AhmadHaniF1145/Projek-Mikrokontroller-Sensor-Gas/Assets/PCB Design/Final/PCB 3D Model/3D Image dengan komponen (tidak lengkap).png

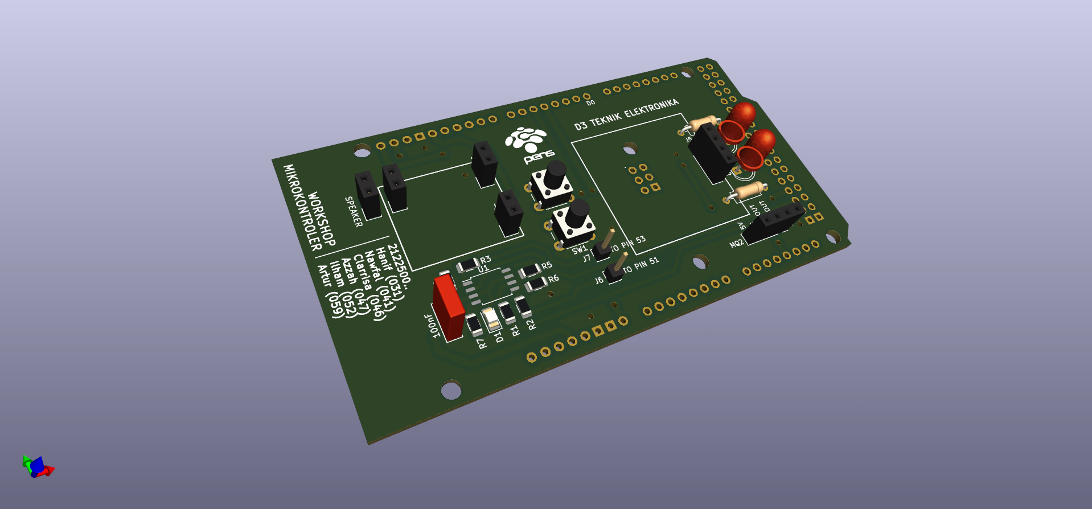
Assets/PCB Design/Final/PCB 3D Model/3D Image dengan komponen (tidak lengkap).png
