AhmadHaniF1145/Projek-Mikrokontroller-Sensor-Gas/Assets/PCB Design/Final/TOP.JPG

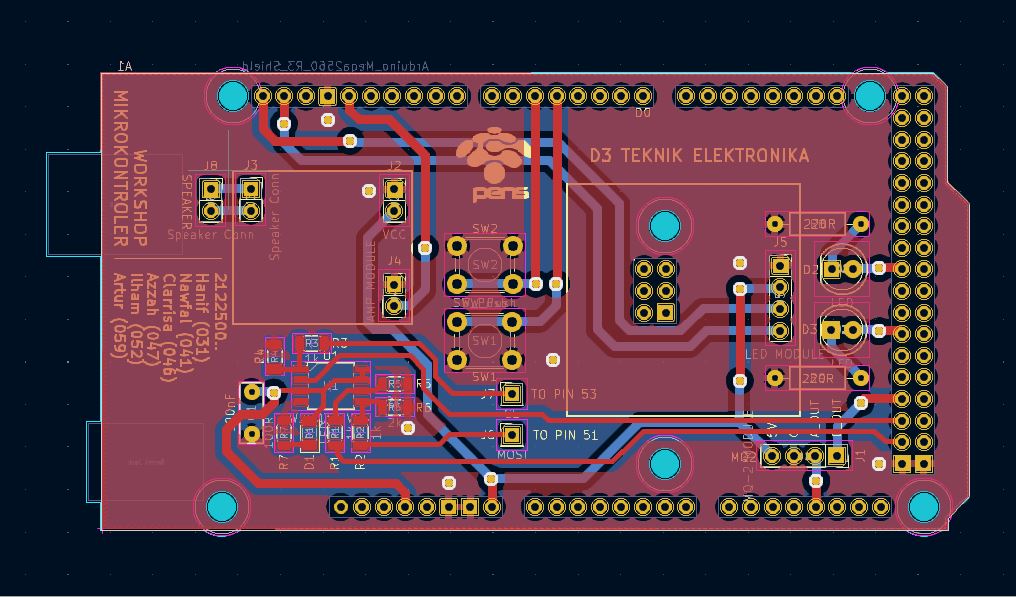
Assets/PCB Design/Final/TOP.JPG
