AhmadHaniF1145/Projek-Mikrokontroller-Sensor-Gas/Assets/PCB Design/Pre/3D PCB Design/1.jpg

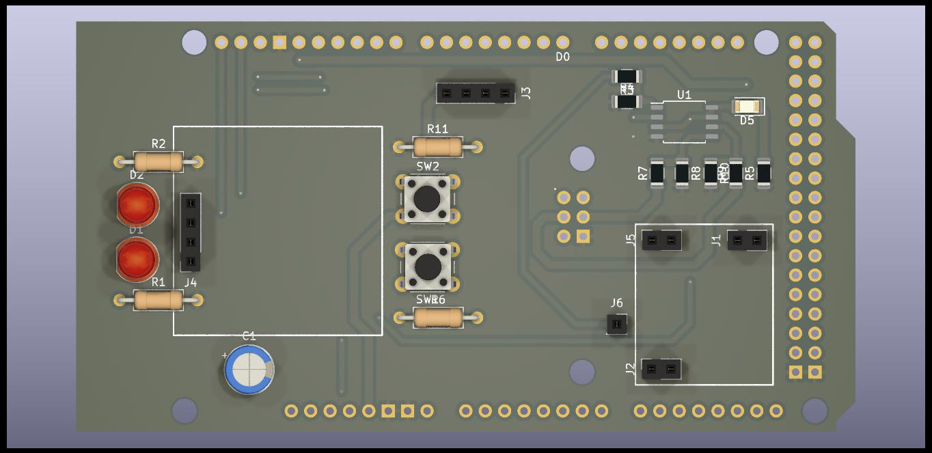
Assets/PCB Design/Pre/3D PCB Design/1.jpg
