AhmadHaniF1145/Projek-Mikrokontroller-Sensor-Gas/Assets/PCB Design/Pre/PCB TOP.JPG

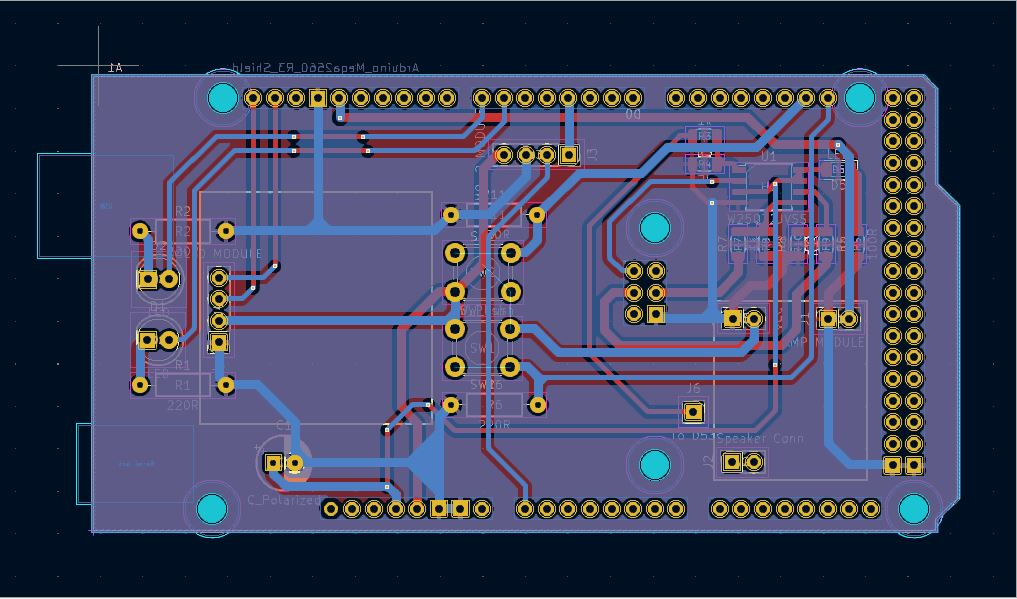
Assets/PCB Design/Pre/PCB TOP.JPG
