AhmadHaniF1145/Projek-Mikrokontroller-Sensor-Gas/Assets/Simulation and Schematic Design/Configuration.jpg

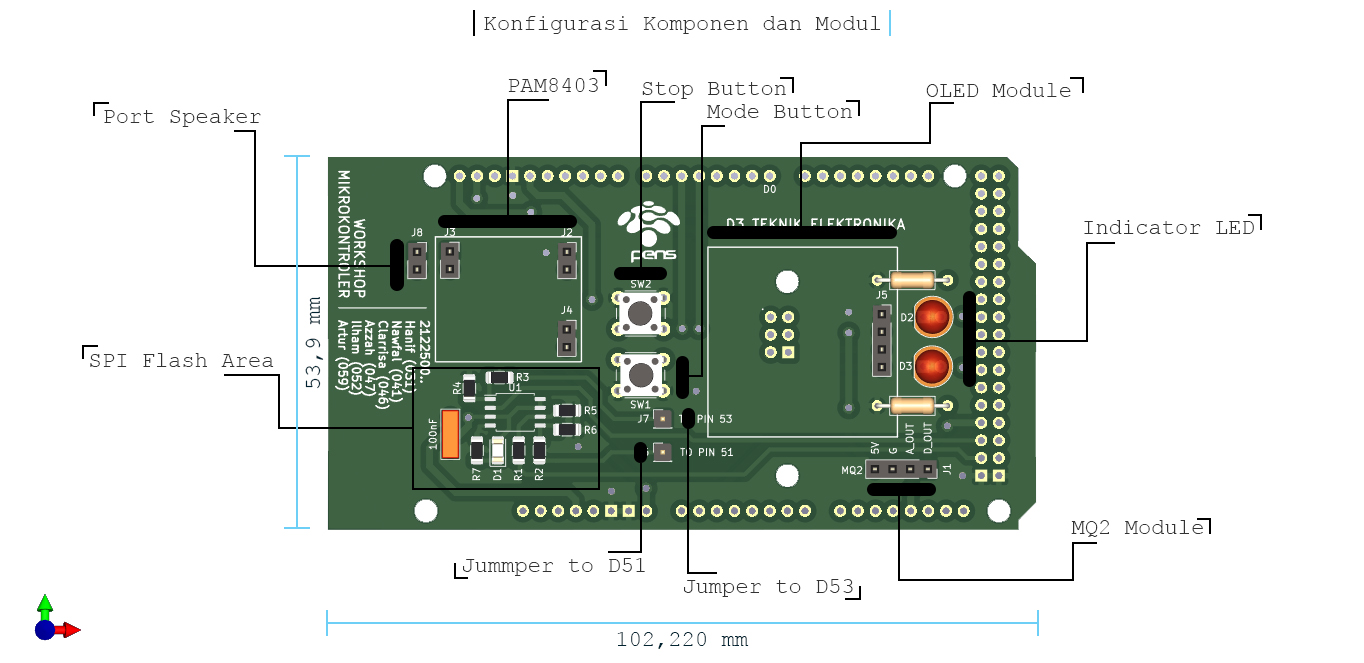
Assets/Simulation and Schematic Design/Configuration.jpg
