AhmadHaniF1145/Projek-Mikrokontroller-Sensor-Gas/Assets/Simulation and Schematic Design/Schematic - Pre.jpg

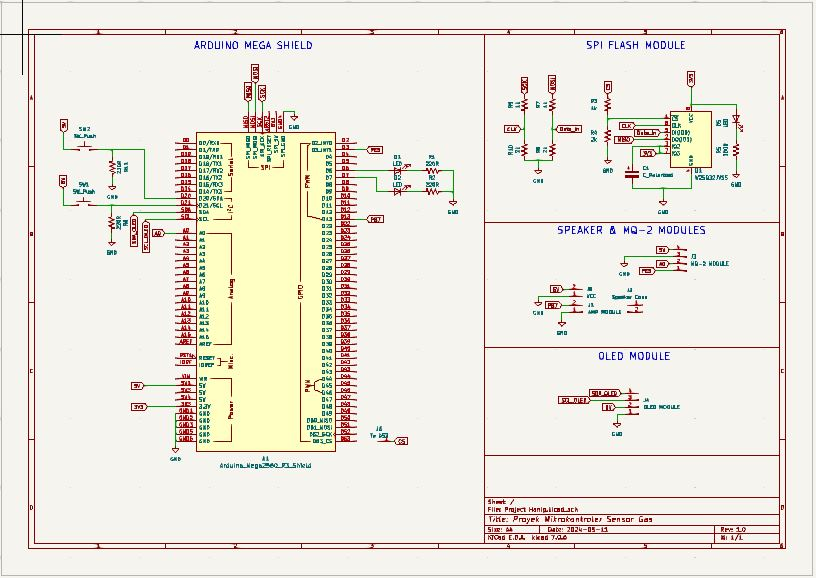
Assets/Simulation and Schematic Design/Schematic - Pre.jpg
