AhmadHaniF1145/Projek-Mikrokontroller-Sensor-Gas/Audio_Project/audio1/audio1 auda.png

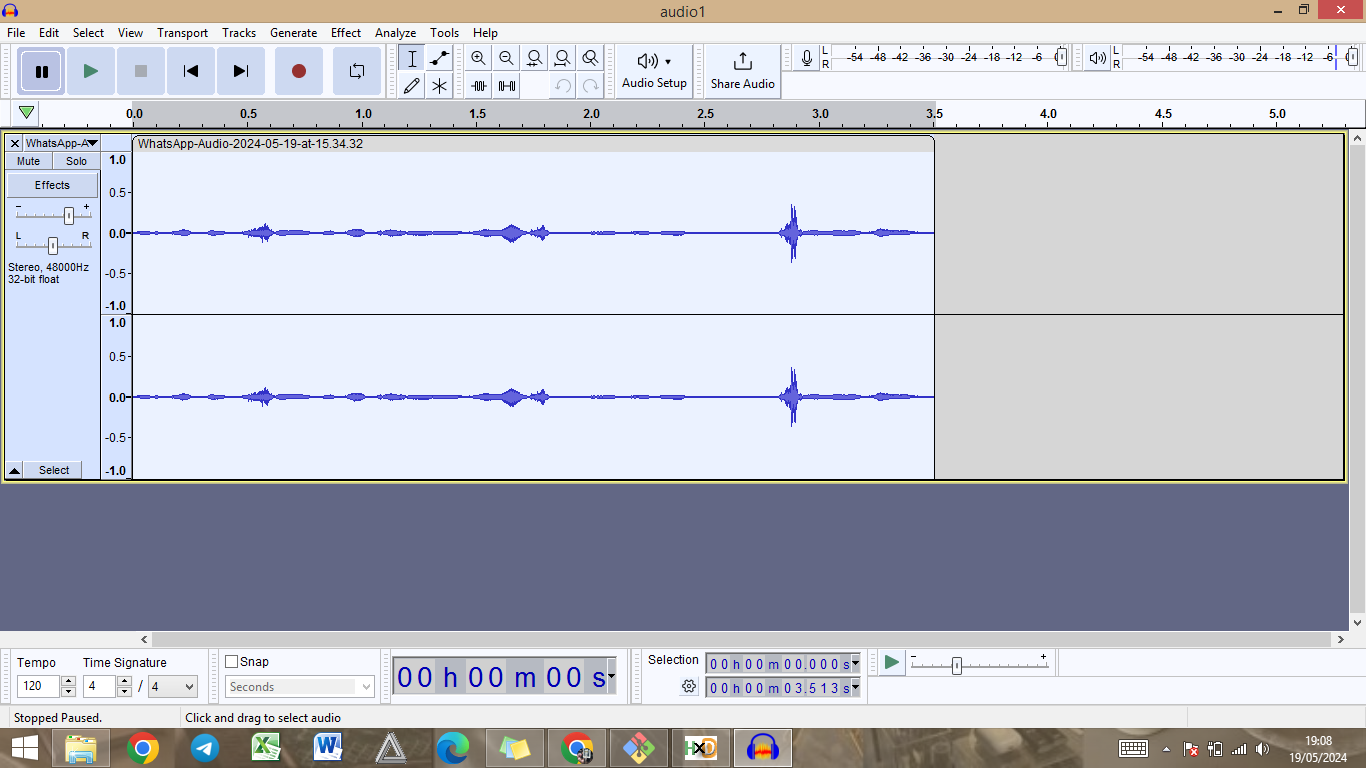
Audio_Project/audio1/audio1 auda.png
