AhmadHaniF1145/Projek-Mikrokontroller-Sensor-Gas/Audio_Project/audio1/audio1 hxd.png

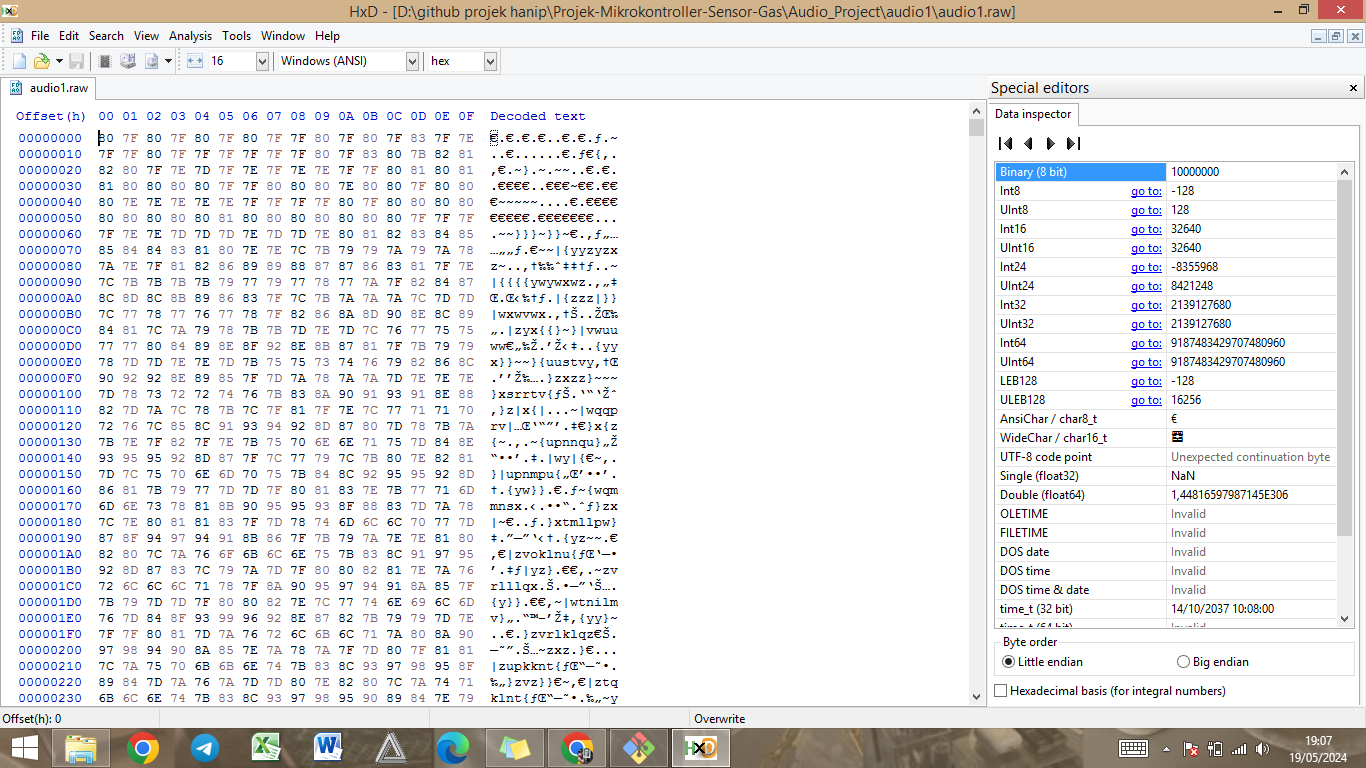
Audio_Project/audio1/audio1 hxd.png
