AhmadHaniF1145/Projek-Mikrokontroller-Sensor-Gas/Audio_Project/audio2/audio2 auda.png

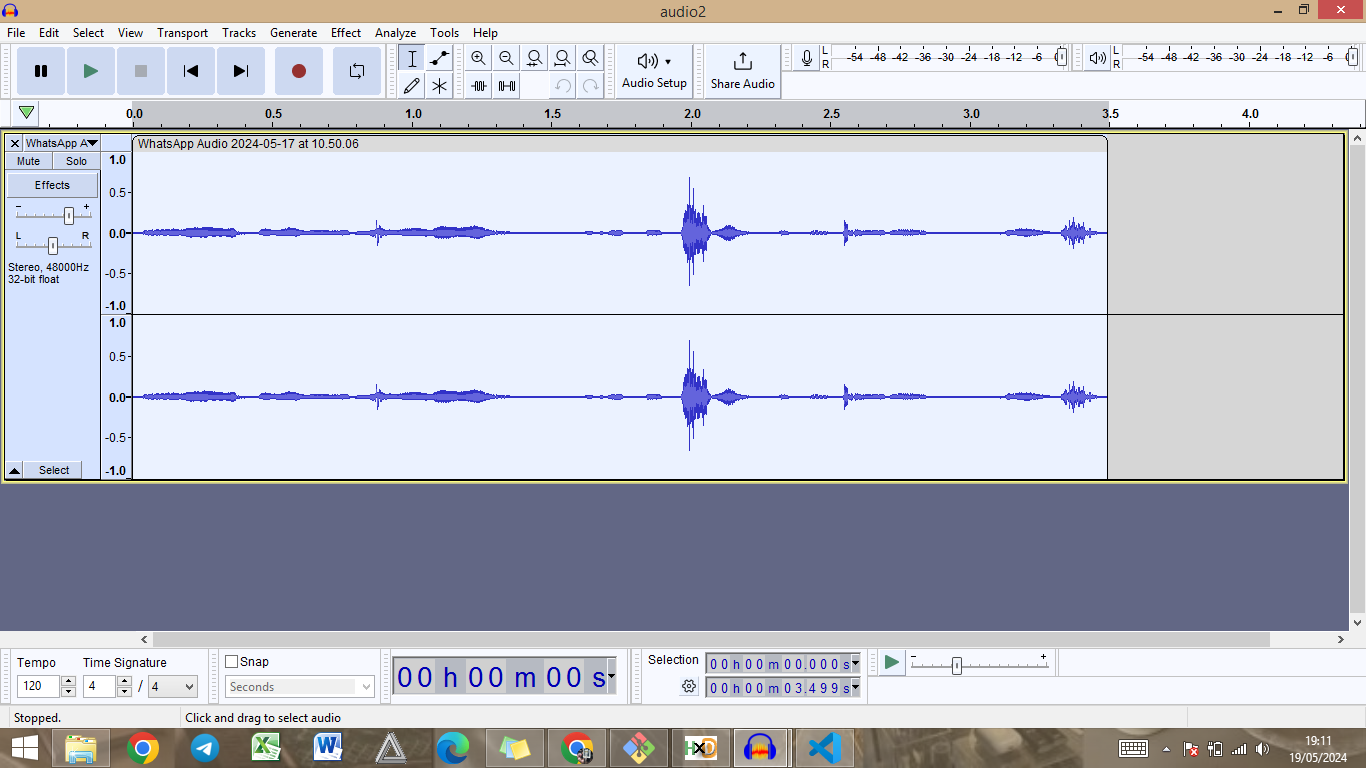
Audio_Project/audio2/audio2 auda.png
