AhmadHaniF1145/Projek-Mikrokontroller-Sensor-Gas/Audio_Project/audio2/audio2 hxd.png

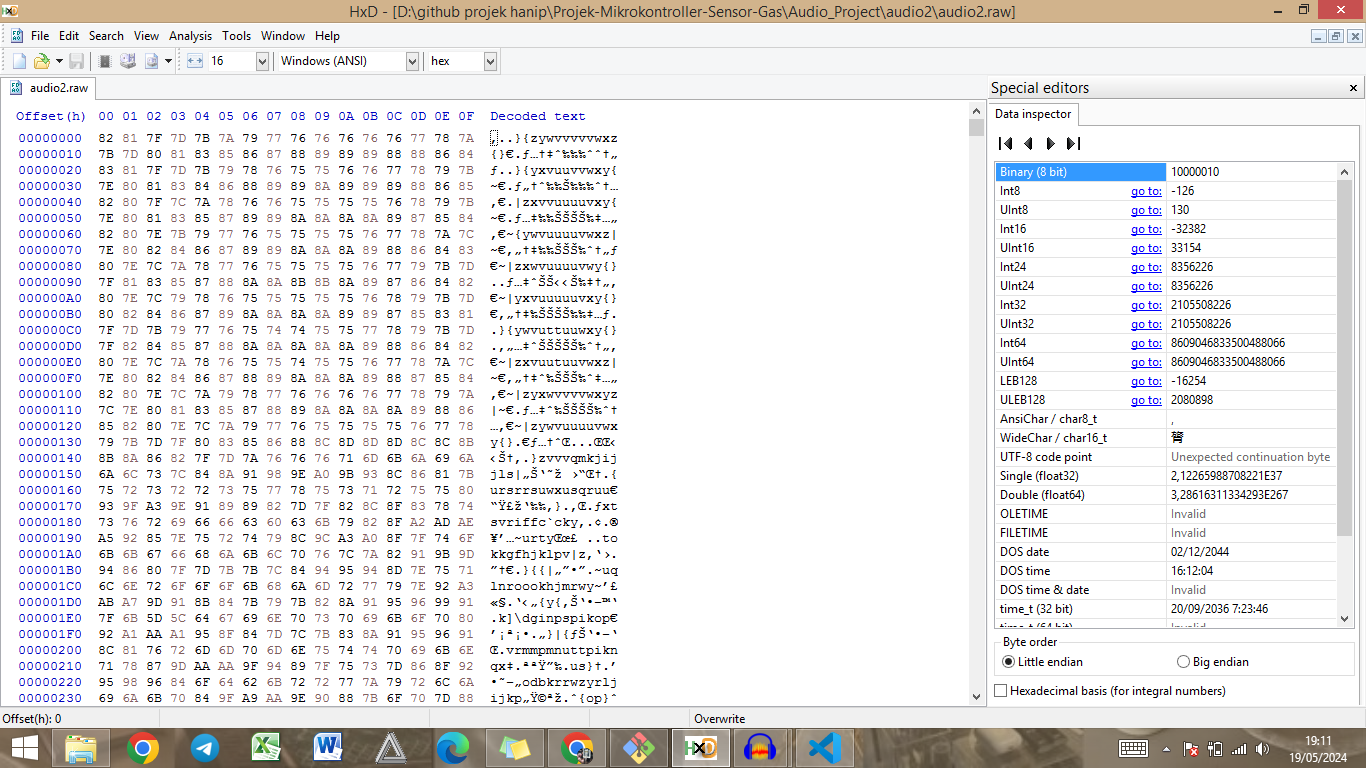
Audio_Project/audio2/audio2 hxd.png
