AhmadHaniF1145/Projek-Mikrokontroller-Sensor-Gas/Desain 3D/Casing 3D Drawing v3.jpg

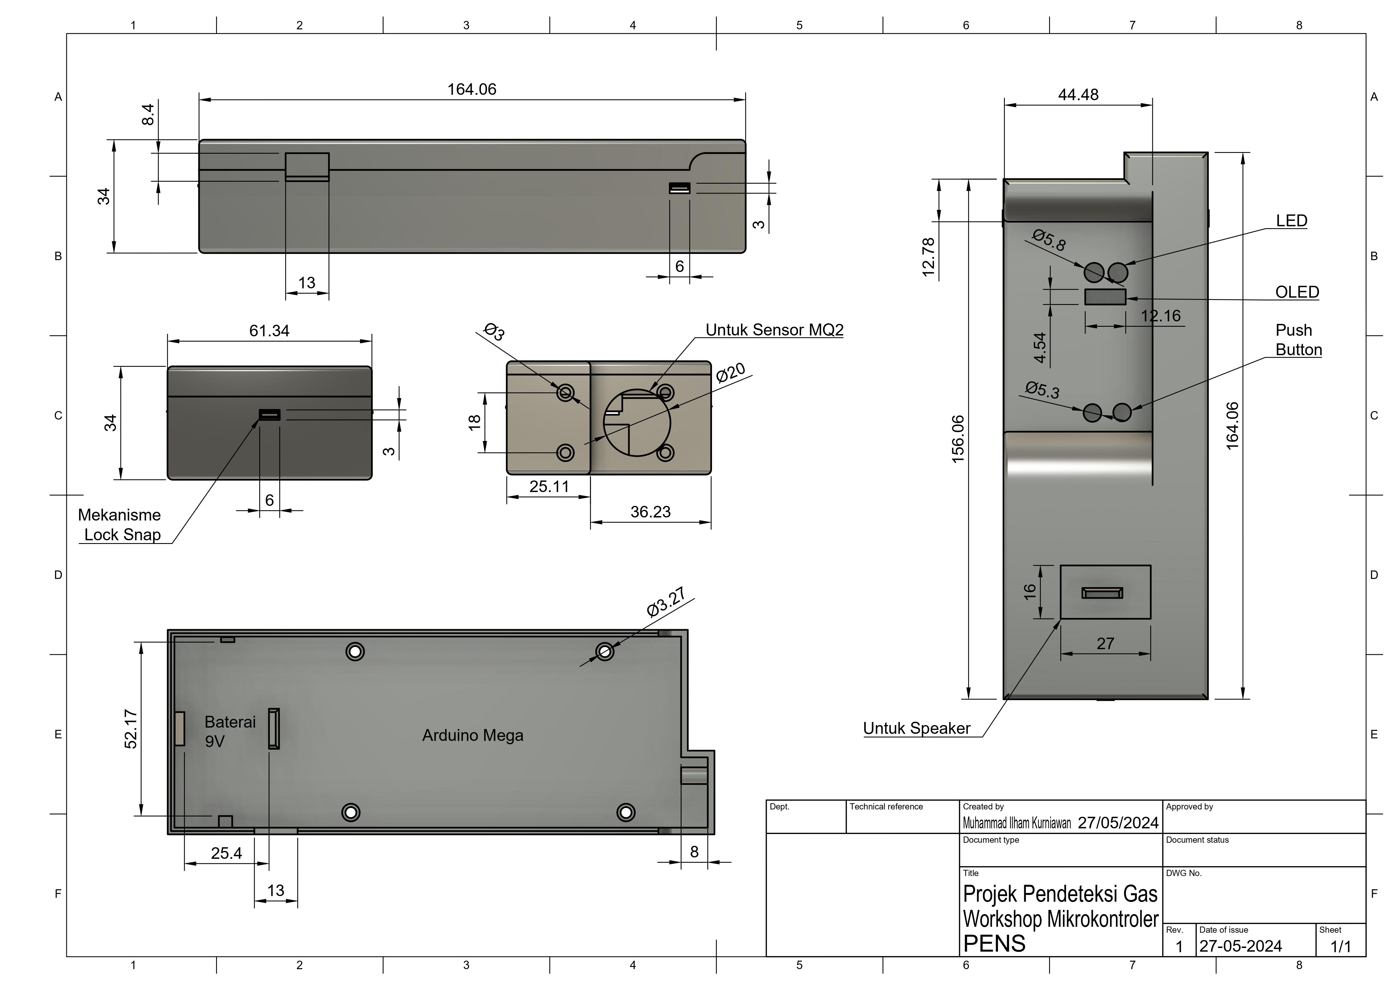
Desain 3D/Casing 3D Drawing v3.jpg
