AhmadHaniF1145/Projek-Mikrokontroller-Sensor-Gas/Desain 3D/Hasil Desain 3D.jpeg

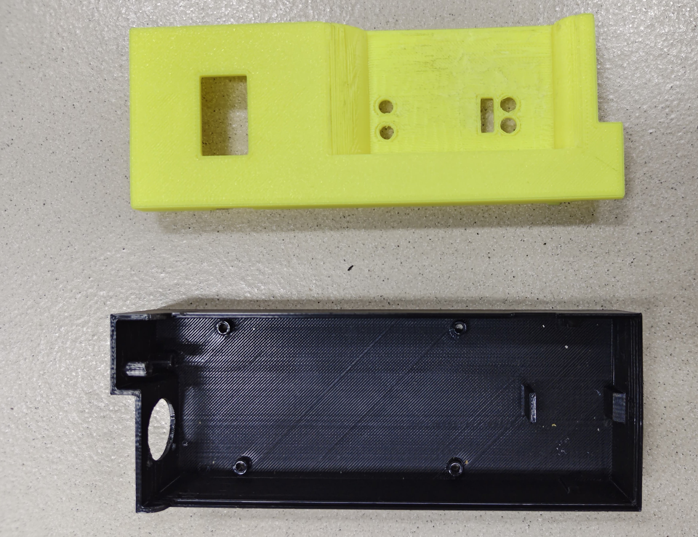
Desain 3D/Hasil Desain 3D.jpeg
