AhmadHaniF1145/Projek-Mikrokontroller-Sensor-Gas/Desain 3D/Prototype 1.png

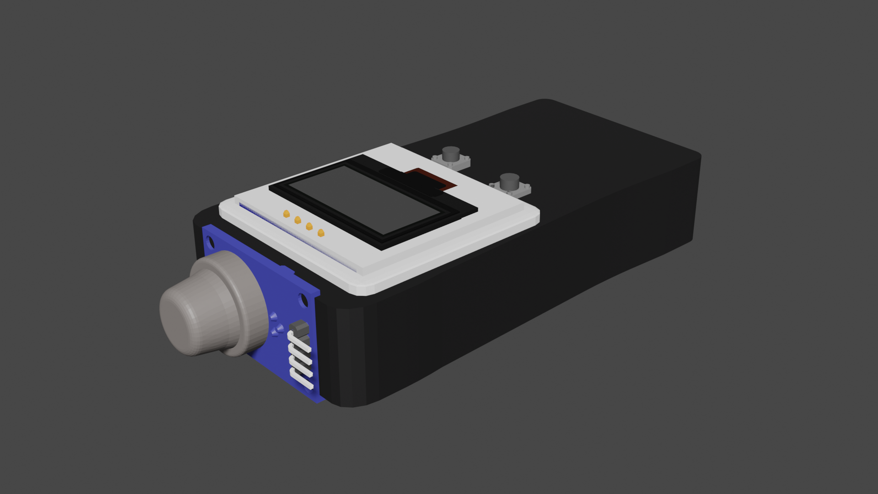
Desain 3D/Prototype 1.png
