AhmadHaniF1145/Projek-Mikrokontroller-Sensor-Gas/Desain 3D/WhatsApp Image 2024-05-21 at 08.23.38.jpeg

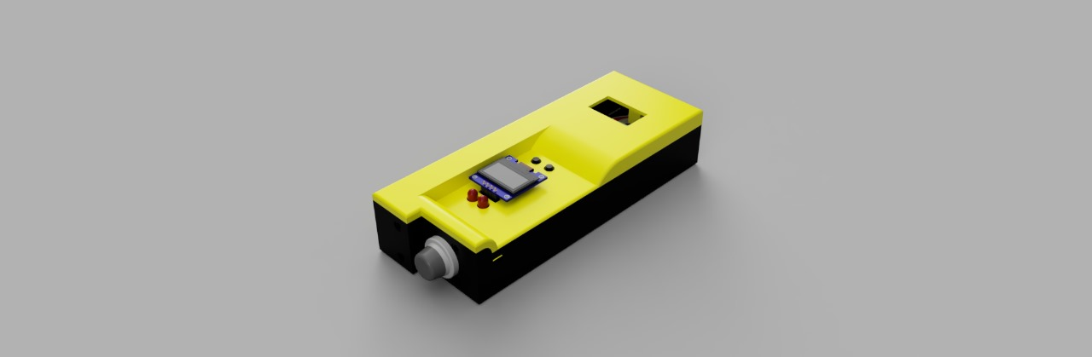
Desain 3D/WhatsApp Image 2024-05-21 at 08.23.38.jpeg
