AhmadHaniF1145/Projek-Mikrokontroller-Sensor-Gas/Dokumentasi/Desain PCB.jpeg

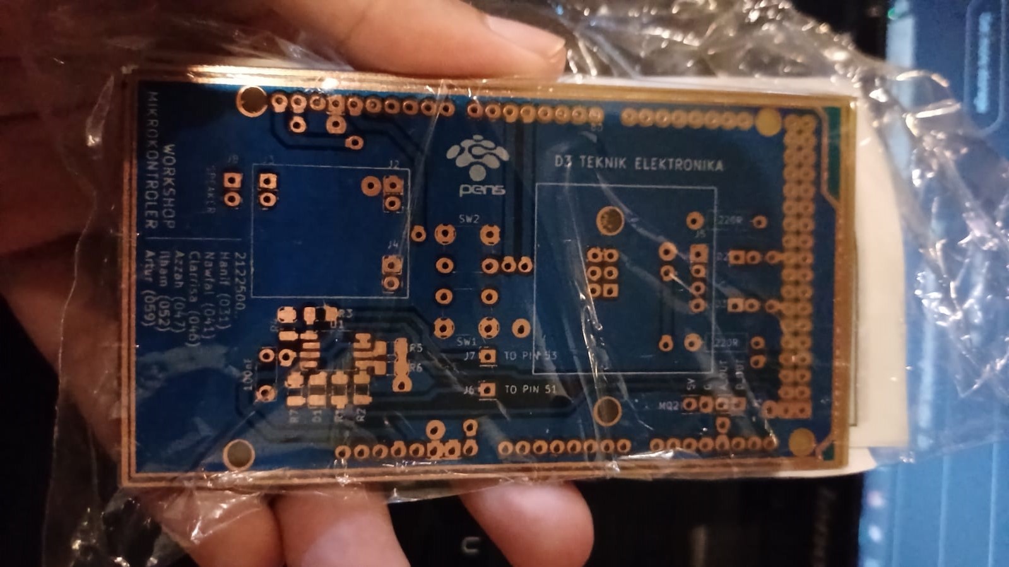
Dokumentasi/Desain PCB.jpeg
