AhmadHaniF1145/Projek-Mikrokontroller-Sensor-Gas/Dokumentasi/Komponen yang Sudah Dibeli.jpeg

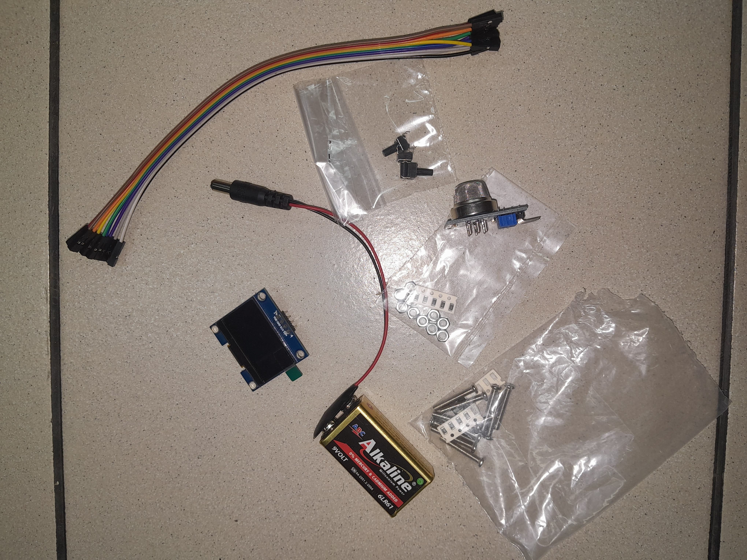
Dokumentasi/Komponen yang Sudah Dibeli.jpeg
