AhmadHaniF1145/Projek-Mikrokontroller-Sensor-Gas/Dokumentasi/Pembuataan Program.jpg

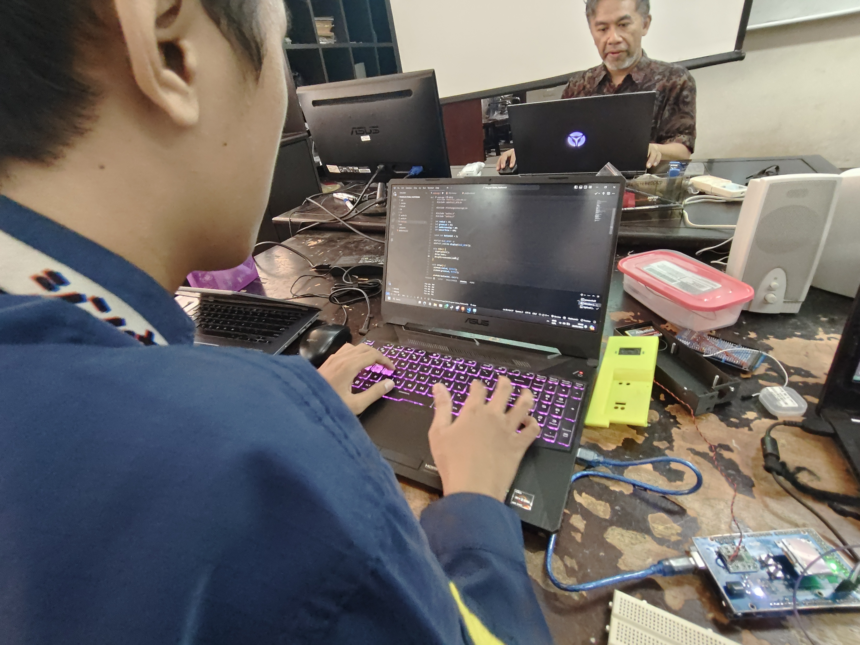
Dokumentasi/Pembuataan Program.jpg
