AhmadHaniF1145/Projek-Mikrokontroller-Sensor-Gas/Dokumentasi/Pembuatan Audio Project.jpeg

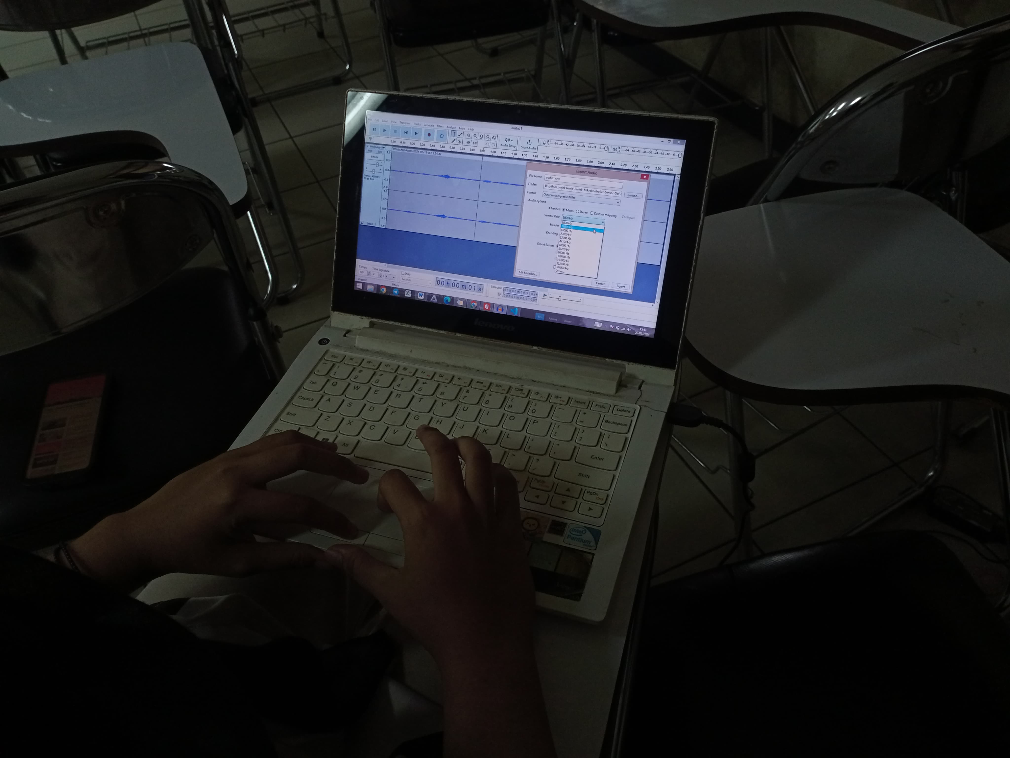
Dokumentasi/Pembuatan Audio Project.jpeg
