AhmadHaniF1145/Projek-Mikrokontroller-Sensor-Gas/Dokumentasi/Pengemasan Project.jpeg

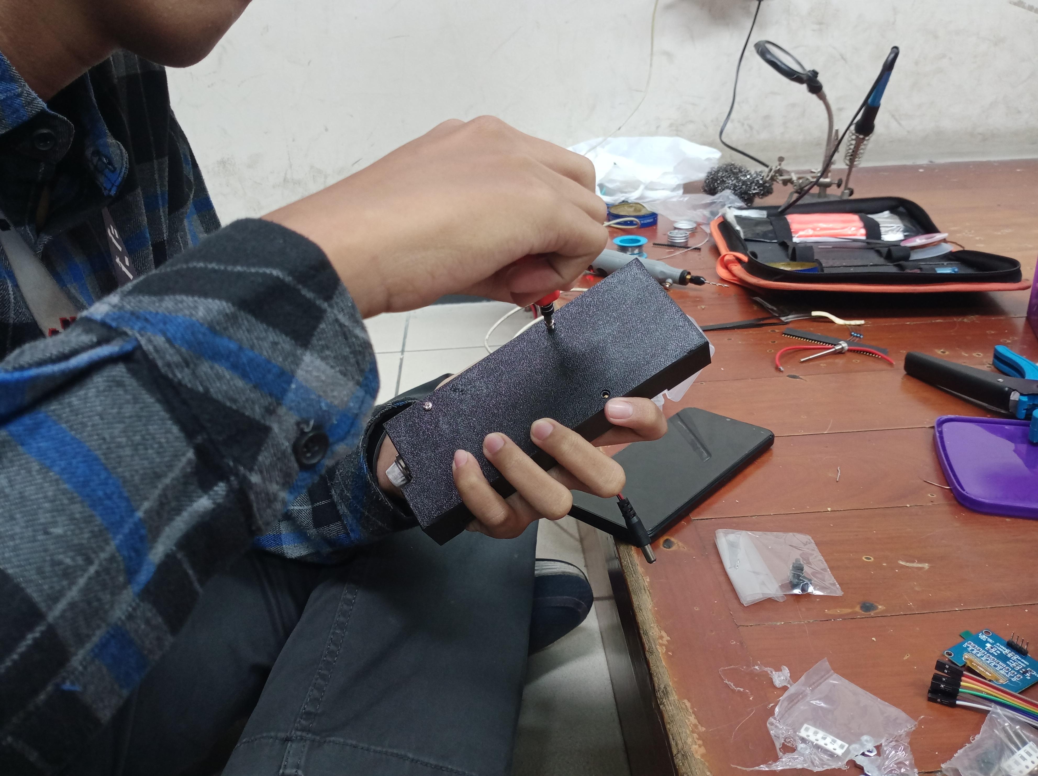
Dokumentasi/Pengemasan Project.jpeg
