AhmadHaniF1145/Projek-Mikrokontroller-Sensor-Gas/Dokumentasi/Pengujian Alat Pada Gas LPG.jpg

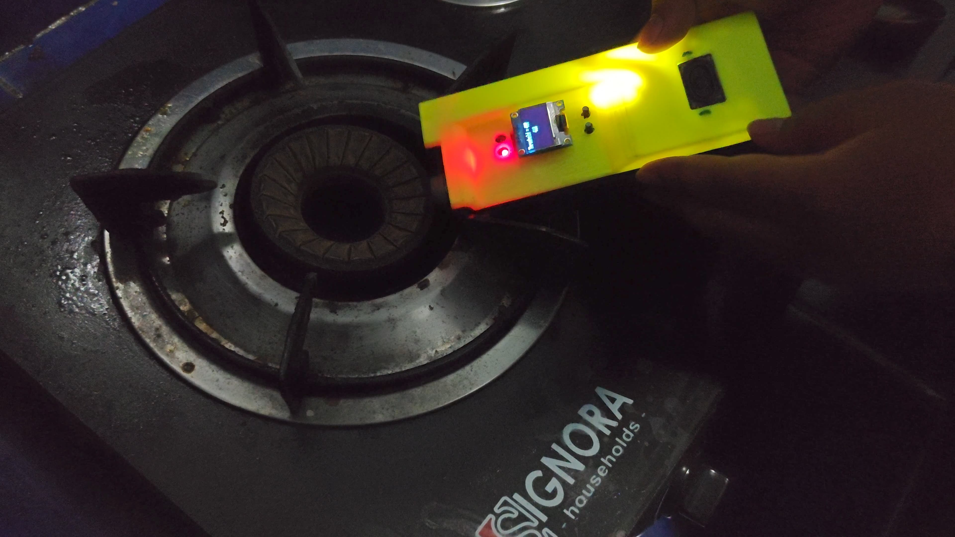
Dokumentasi/Pengujian Alat Pada Gas LPG.jpg
