AhmadHaniF1145/Projek-Mikrokontroller-Sensor-Gas/Dokumentasi/Pengujian Alat.jpg

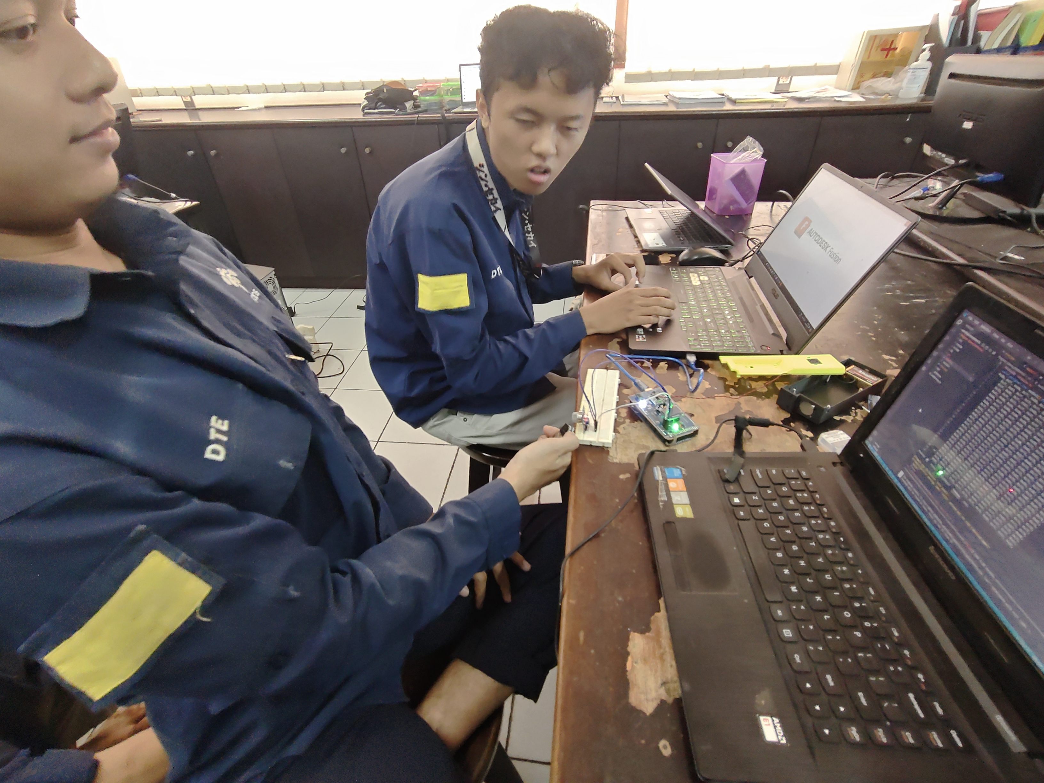
Dokumentasi/Pengujian Alat.jpg
