AhmadHaniF1145/Projek-Mikrokontroller-Sensor-Gas/Dokumentasi/Pengujian Pada Software.jpg

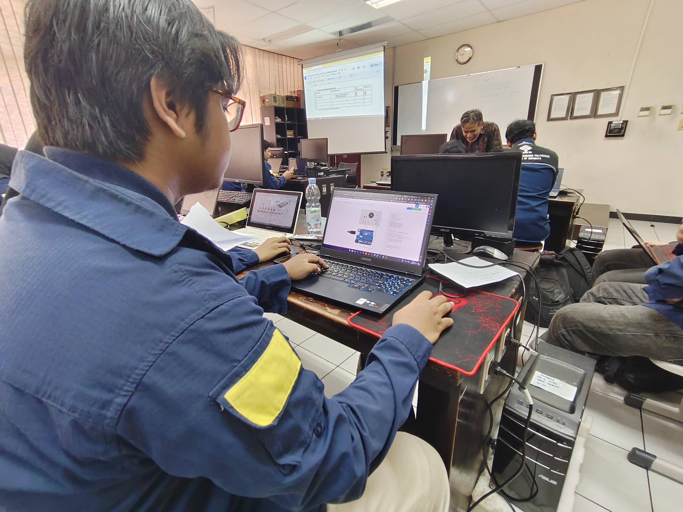
Dokumentasi/Pengujian Pada Software.jpg
