AhmadHaniF1145/Projek-Mikrokontroller-Sensor-Gas/Dokumentasi/Proses Penyolderan.jpeg

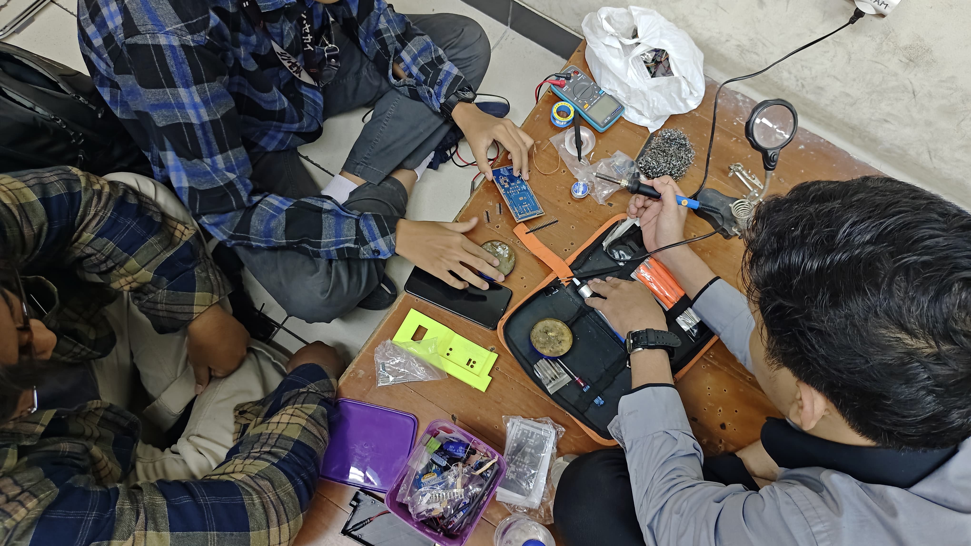
Dokumentasi/Proses Penyolderan.jpeg
