AhmadHaniF1145/Projek-Mikrokontroller-Sensor-Gas/Dokumentasi/Publikasi pada Github.jpeg

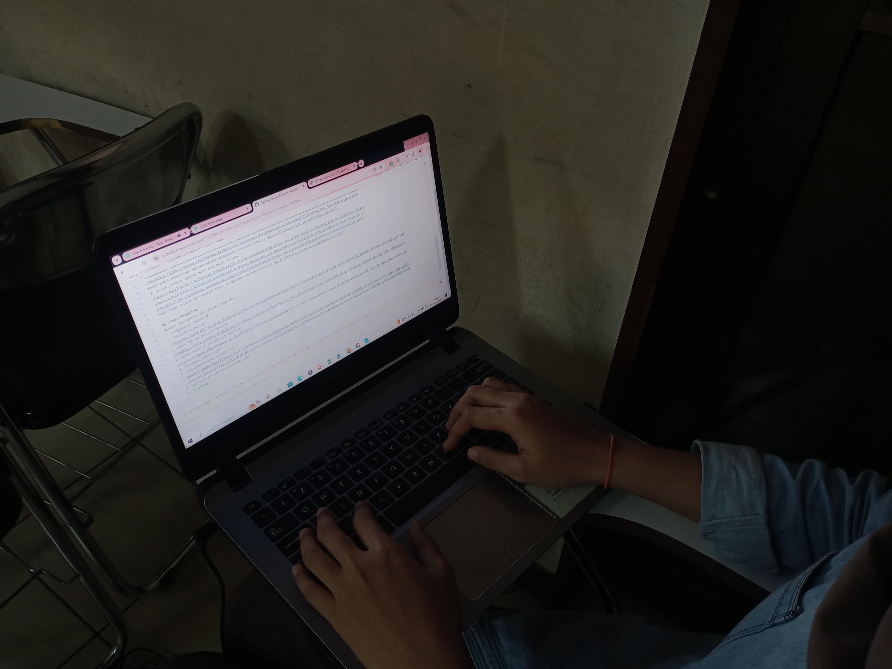
Dokumentasi/Publikasi pada Github.jpeg
