AhmadHaniF1145/Projek-Mikrokontroller-Sensor-Gas/Dokumentasi/Publikasi Thingverse.png

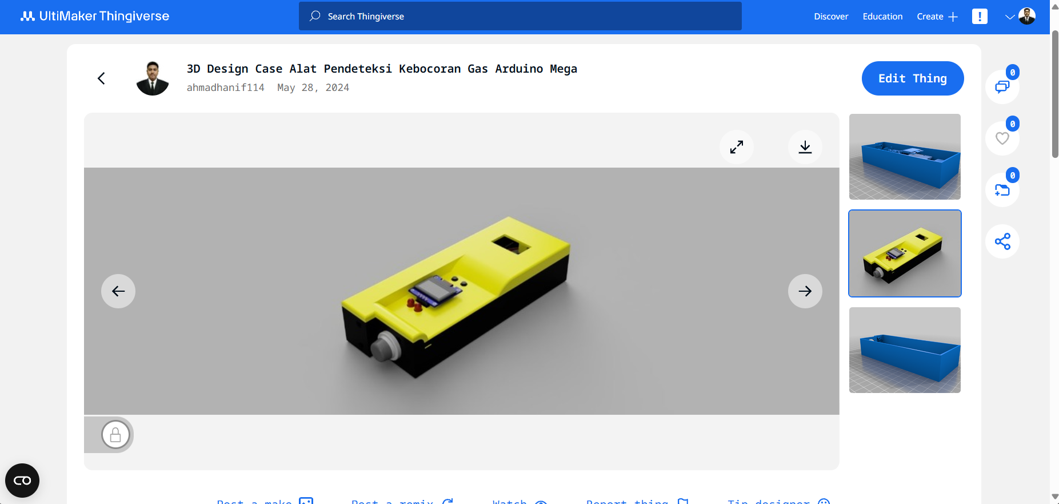
Dokumentasi/Publikasi Thingverse.png
