AhmadHaniF1145/Projek-Mikrokontroller-Sensor-Gas/Dokumentasi/Studi Literatur.jpg

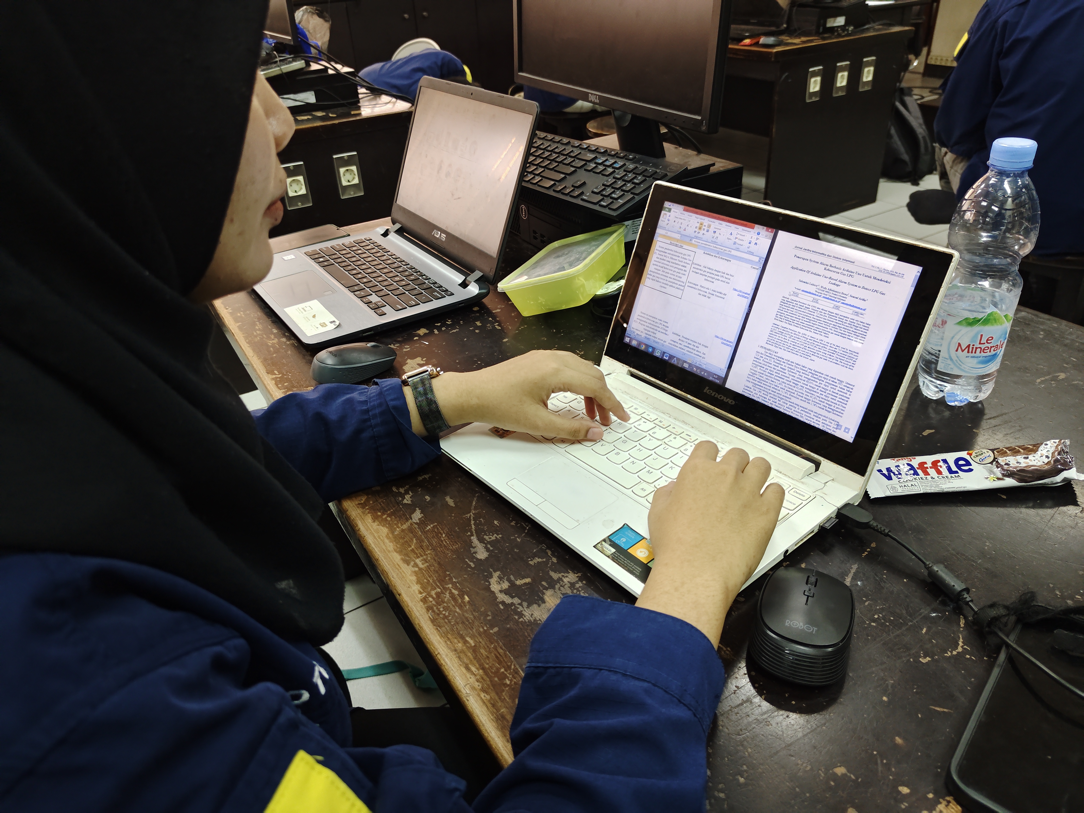
Dokumentasi/Studi Literatur.jpg
