AhmadHaniF1145/Projek-Mikrokontroller-Sensor-Gas/PCB Board/Progress 1/Diagram.JPG

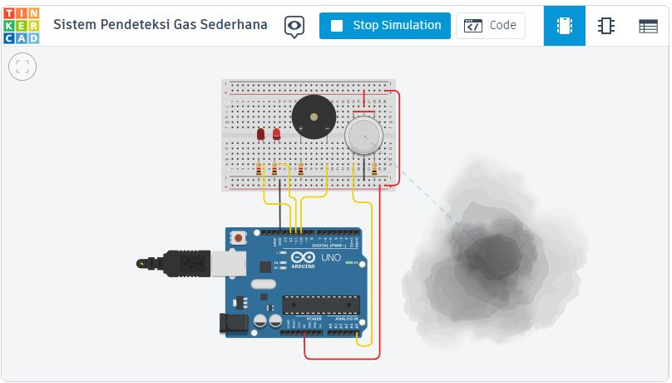
PCB Board/Progress 1/Diagram.JPG
