AhmadHaniF1145/Projek-Mikrokontroller-Sensor-Gas/Desain 3D/Fusion 360 (Manufacture)/Casing_3D_2024-May-12_09-13-18AM-000_CustomizedView19460723771.png

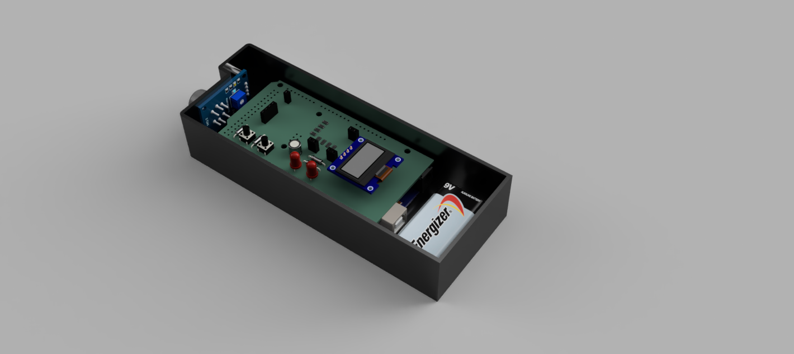
Desain 3D/Fusion 360 (Manufacture)/Casing_3D_2024-May-12_09-13-18AM-000_CustomizedView19460723771.png
