AhmadHaniF1145/Projek-Mikrokontroller-Sensor-Gas/Desain 3D/Fusion 360 (Manufacture)/Casing_3D_2024-May-12_09-14-30AM-000_CustomizedView43419546548.png

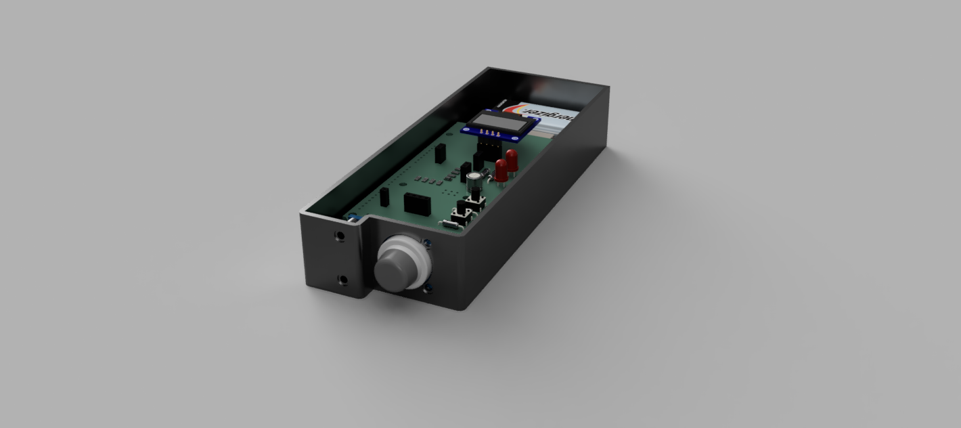
Desain 3D/Fusion 360 (Manufacture)/Casing_3D_2024-May-12_09-14-30AM-000_CustomizedView43419546548.png
