AhmadHaniF1145/Projek-Mikrokontroller-Sensor-Gas/Desain 3D/Fusion 360 (Manufacture)/Casing_3D_2024-May-12_09-15-01AM-000_CustomizedView60361281327.png

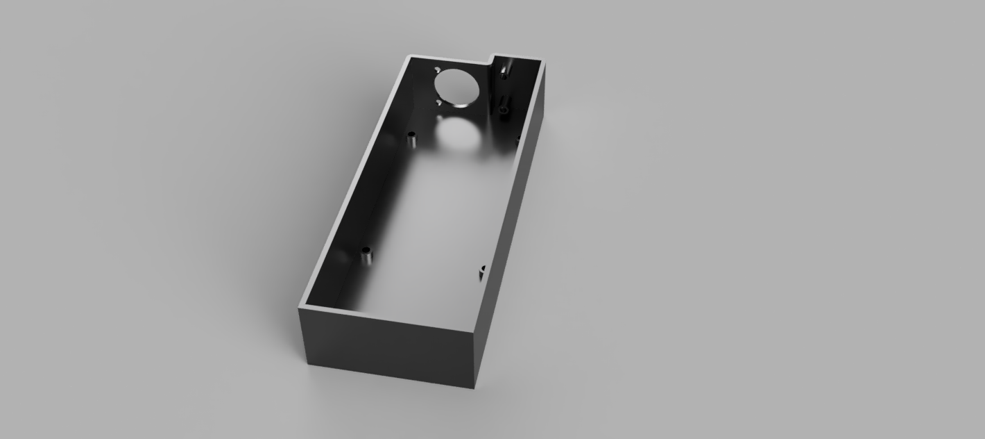
Desain 3D/Fusion 360 (Manufacture)/Casing_3D_2024-May-12_09-15-01AM-000_CustomizedView60361281327.png
