AhmadHaniF1145/Projek-Mikrokontroller-Sensor-Gas/Desain 3D/Fusion 360 (Manufacture)/Screenshot (462).png

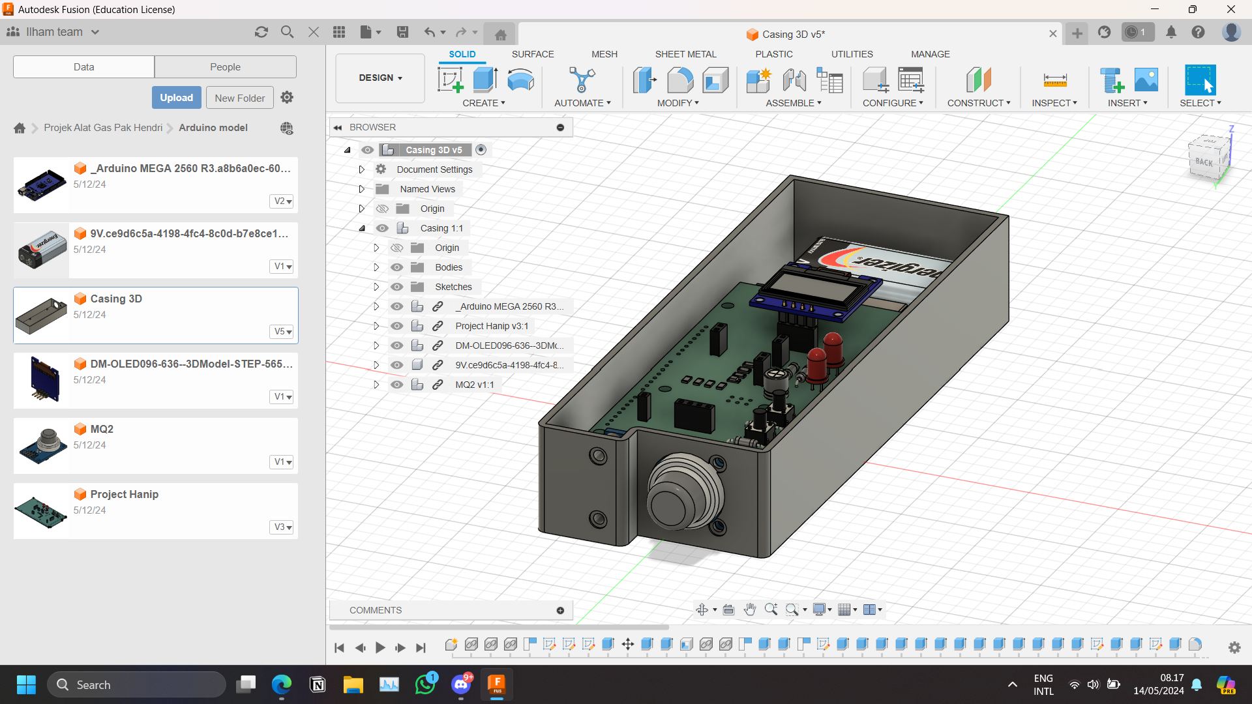
Desain 3D/Fusion 360 (Manufacture)/Screenshot (462).png
