AhmadHaniF1145/Projek-Mikrokontroller-Sensor-Gas/Desain 3D/Fusion 360 (Manufacture)/Screenshot (463).png

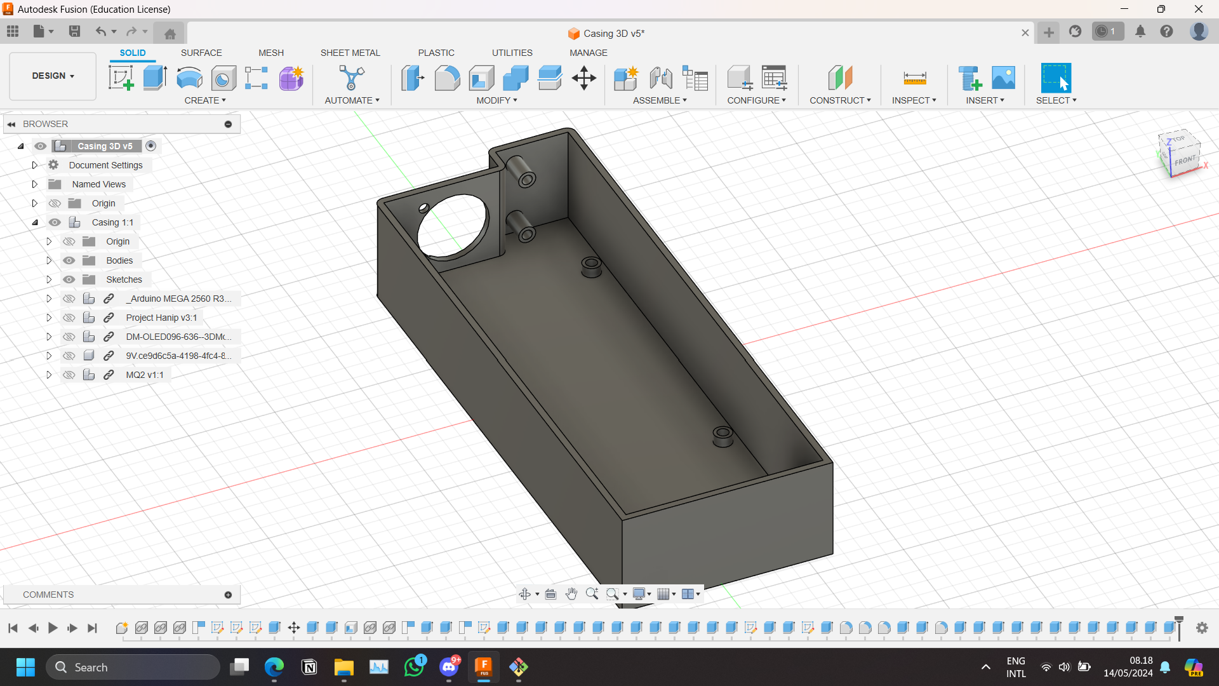
Desain 3D/Fusion 360 (Manufacture)/Screenshot (463).png
