AhmadHaniF1145/Projek-Mikrokontroller-Sensor-Gas/Assets/PCB Print/Rev 0/PCB Top Silk.pdf

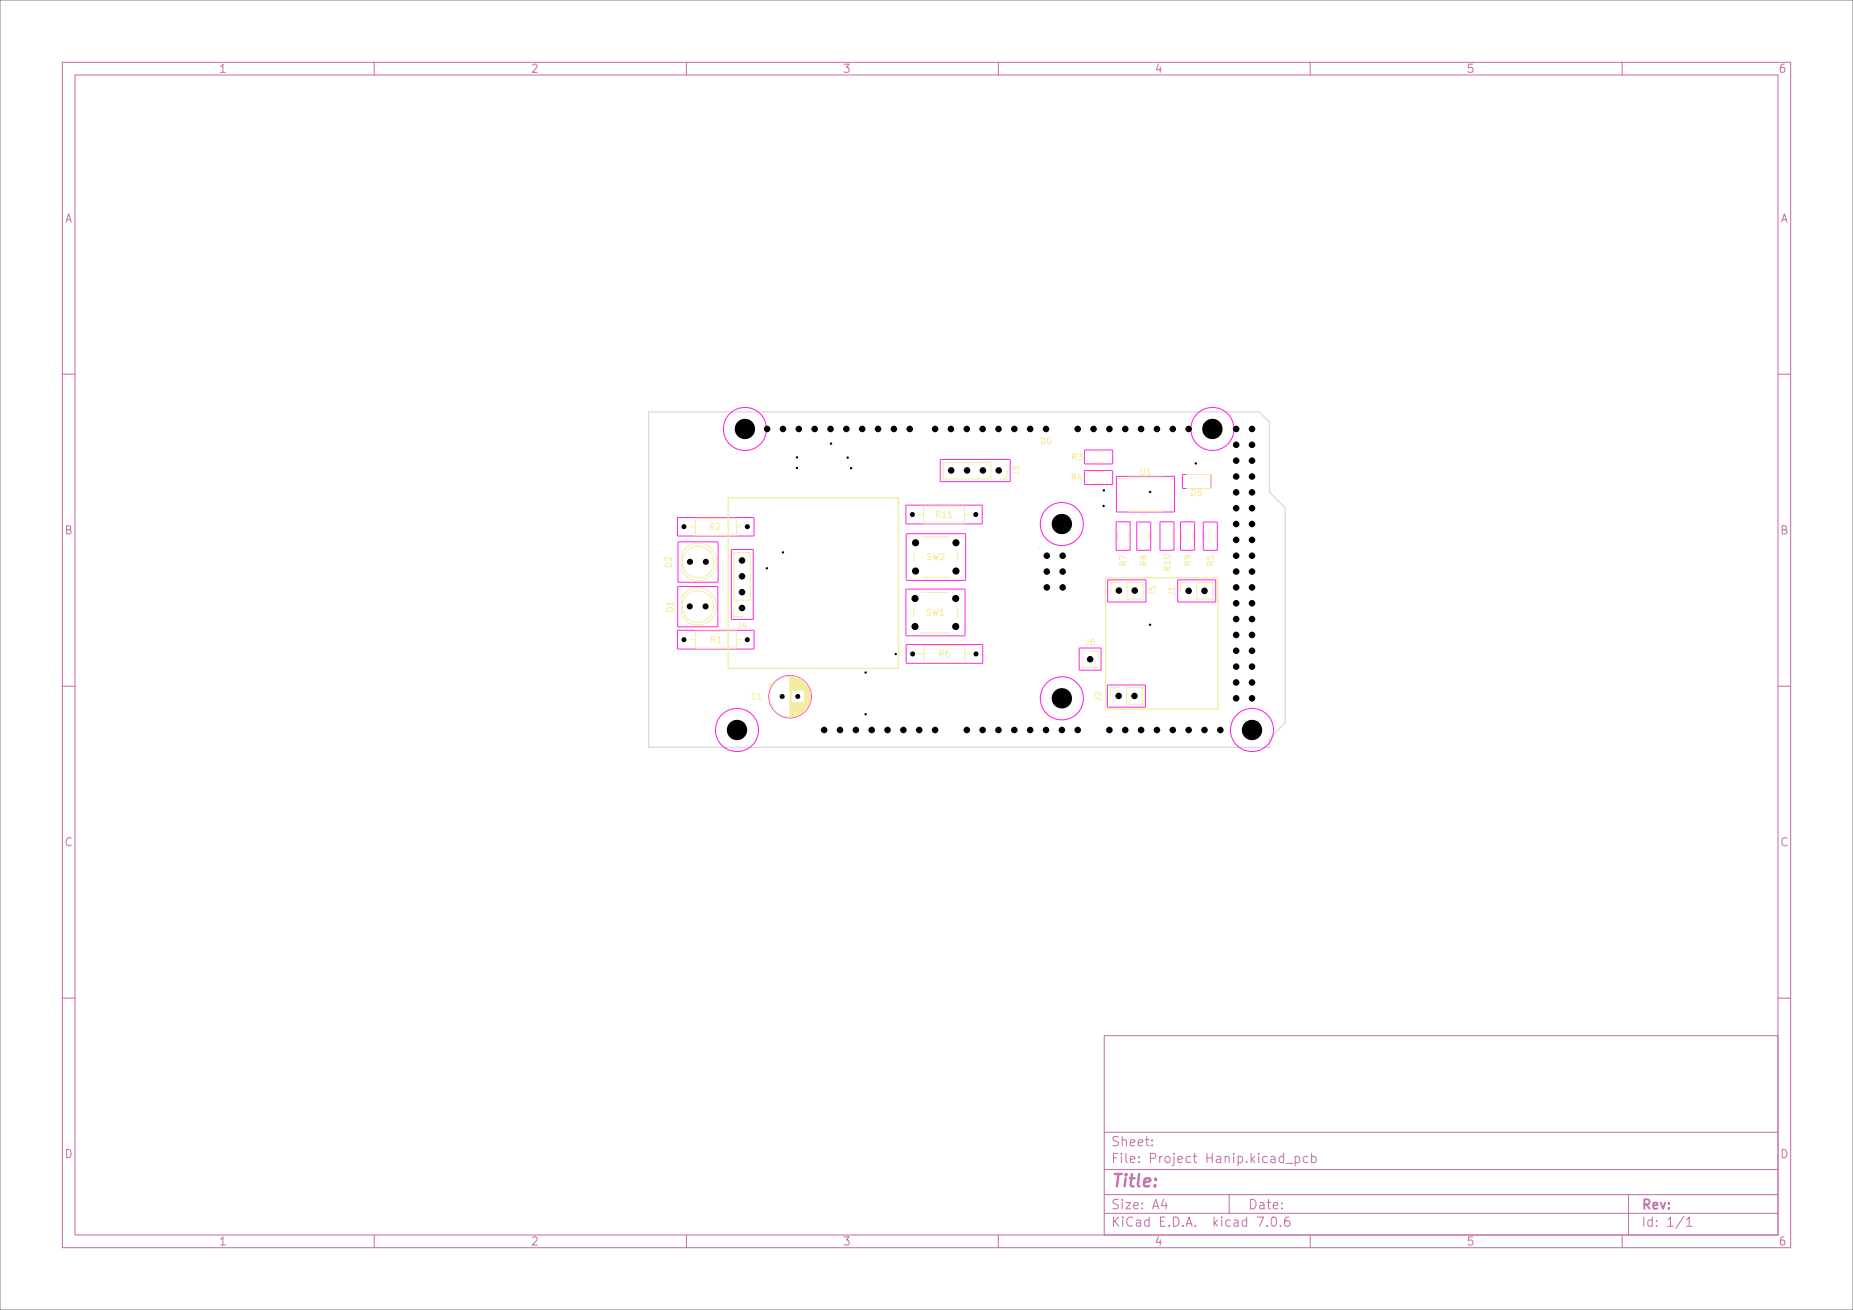
[picture p62: page 1]
