AhmadHaniF1145/Projek-Mikrokontroller-Sensor-Gas/Assets/PCB Print/Rev 0/PCB Top.pdf

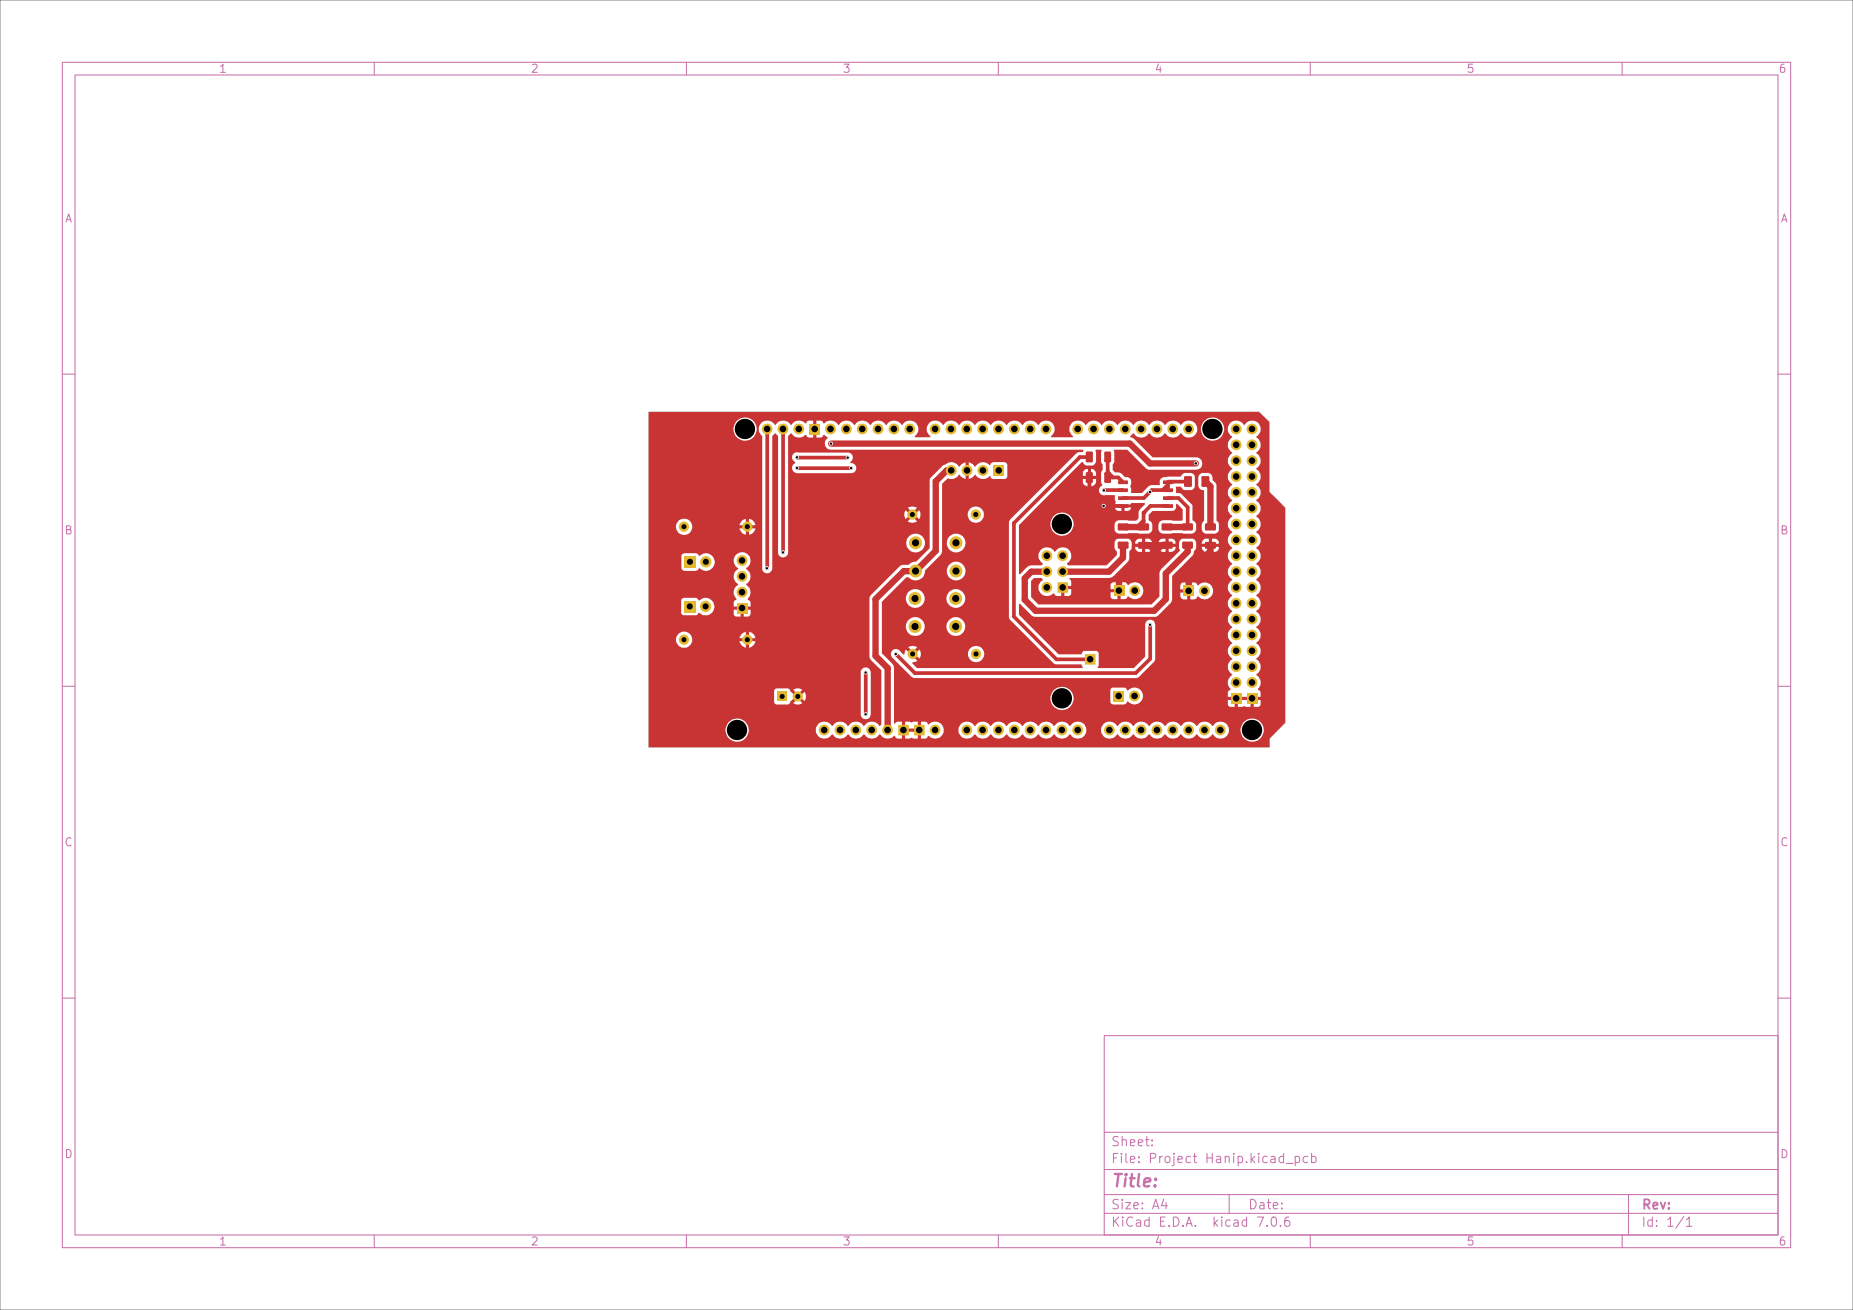
[picture p63: page 1]
