AhmadHaniF1145/Projek-Mikrokontroller-Sensor-Gas/ProgramUtama/Program Utama_Bare Metal_PlatformIO/src/audio1.h

#include <Arduino.h>

const unsigned char audio1[] PROGMEM = {
0x80, 0x7F, 0x80, 0x7F, 0x80, 0x7F, 0x80, 0x7F, 0x7F, 0x80, 0x7F, 0x80,
	0x7F, 0x83, 0x7F, 0x7E, 0x7F, 0x7F, 0x80, 0x7F, 0x7F, 0x7F, 0x7F, 0x7F,
	0x7F, 0x80, 0x7F, 0x83, 0x80, 0x7B, 0x82, 0x81, 0x82, 0x80, 0x7F, 0x7E,
	0x7D, 0x7F, 0x7E, 0x7F, 0x7E, 0x7E, 0x7F, 0x7F, 0x80, 0x81, 0x80, 0x81,
	0x81, 0x80, 0x80, 0x80, 0x80, 0x7F, 0x7F, 0x80, 0x80, 0x80, 0x7E, 0x80,
	0x80, 0x7F, 0x80, 0x80, 0x80, 0x7E, 0x7E, 0x7E, 0x7E, 0x7E, 0x7F, 0x7F,
	0x7F, 0x7F, 0x80, 0x7F, 0x80, 0x80, 0x80, 0x80, 0x80, 0x80, 0x80, 0x80,
	0x80, 0x81, 0x80, 0x80, 0x80, 0x80, 0x80, 0x80, 0x80, 0x7F, 0x7F, 0x7F,
	0x7F, 0x7E, 0x7E, 0x7D, 0x7D, 0x7D, 0x7E, 0x7D, 0x7D, 0x7E, 0x80, 0x81,
	0x82, 0x83, 0x84, 0x85, 0x85, 0x84, 0x84, 0x83, 0x81, 0x80, 0x7E, 0x7E,
	0x7C, 0x7B, 0x79, 0x79, 0x7A, 0x79, 0x7A, 0x78, 0x7A, 0x7E, 0x7F, 0x81,
	0x82, 0x86, 0x89, 0x89, 0x88, 0x87, 0x87, 0x86, 0x83, 0x81, 0x7F, 0x7E,
	0x7C, 0x7B, 0x7B, 0x7B, 0x7B, 0x79, 0x77, 0x79, 0x77, 0x78, 0x77, 0x7A,
	0x7F, 0x82, 0x84, 0x87, 0x8C, 0x8D, 0x8C, 0x8B, 0x89, 0x86, 0x83, 0x7F,
	0x7C, 0x7B, 0x7A, 0x7A, 0x7A, 0x7C, 0x7D, 0x7D, 0x7C, 0x77, 0x78, 0x77,
	0x76, 0x77, 0x78, 0x7F, 0x82, 0x86, 0x8A, 0x8D, 0x90, 0x8E, 0x8C, 0x89,
	0x84, 0x81, 0x7C, 0x7A, 0x79, 0x78, 0x7B, 0x7B, 0x7D, 0x7E, 0x7D, 0x7C,
	0x76, 0x77, 0x75, 0x75, 0x77, 0x77, 0x80, 0x84, 0x89, 0x8E, 0x8F, 0x92,
	0x8E, 0x8B, 0x87, 0x81, 0x7F, 0x7B, 0x79, 0x79, 0x78, 0x7D, 0x7D, 0x7E,
	0x7E, 0x7D, 0x7B, 0x75, 0x75, 0x73, 0x74, 0x76, 0x79, 0x82, 0x86, 0x8C,
	0x90, 0x92, 0x92, 0x8E, 0x89, 0x85, 0x7F, 0x7D, 0x7A, 0x78, 0x7A, 0x7A,
	0x7D, 0x7E, 0x7E, 0x7E, 0x7D, 0x78, 0x73, 0x72, 0x72, 0x74, 0x76, 0x7B,
	0x83, 0x8A, 0x90, 0x91, 0x93, 0x91, 0x8E, 0x88, 0x82, 0x7D, 0x7A, 0x7C,
	0x78, 0x7B, 0x7C, 0x7F, 0x81, 0x7F, 0x7E, 0x7C, 0x77, 0x71, 0x71, 0x70,
	0x72, 0x76, 0x7C, 0x85, 0x8C, 0x91, 0x93, 0x94, 0x92, 0x8D, 0x87, 0x80,
	0x7D, 0x78, 0x7B, 0x7A, 0x7B, 0x7E, 0x7F, 0x82, 0x7F, 0x7E, 0x7B, 0x75,
	0x70, 0x6E, 0x6E, 0x71, 0x75, 0x7D, 0x84, 0x8E, 0x93, 0x95, 0x95, 0x92,
	0x8D, 0x87, 0x7F, 0x7C, 0x77, 0x79, 0x7C, 0x7B, 0x80, 0x7E, 0x82, 0x81,
	0x7D, 0x7C, 0x75, 0x70, 0x6E, 0x6D, 0x70, 0x75, 0x7B, 0x84, 0x8C, 0x92,
	0x95, 0x95, 0x92, 0x8D, 0x86, 0x81, 0x7B, 0x79, 0x77, 0x7D, 0x7D, 0x7F,
	0x80, 0x81, 0x83, 0x7E, 0x7B, 0x77, 0x71, 0x6D, 0x6D, 0x6E, 0x73, 0x78,
	0x81, 0x8B, 0x90, 0x95, 0x95, 0x93, 0x8F, 0x88, 0x83, 0x7D, 0x7A, 0x78,
	0x7C, 0x7E, 0x80, 0x81, 0x81, 0x83, 0x7F, 0x7D, 0x78, 0x74, 0x6D, 0x6C,
	0x6C, 0x70, 0x77, 0x7D, 0x87, 0x8F, 0x94, 0x97, 0x94, 0x91, 0x8B, 0x86,
	0x7F, 0x7B, 0x79, 0x7A, 0x7E, 0x7E, 0x81, 0x80, 0x82, 0x80, 0x7C, 0x7A,
	0x76, 0x6F, 0x6B, 0x6C, 0x6E, 0x75, 0x7B, 0x83, 0x8C, 0x91, 0x97, 0x95,
	0x92, 0x8D, 0x87, 0x83, 0x7C, 0x79, 0x7A, 0x7D, 0x7F, 0x80, 0x80, 0x82,
	0x81, 0x7E, 0x7A, 0x76, 0x72, 0x6C, 0x6C, 0x6C, 0x71, 0x78, 0x7F, 0x8A,
	0x90, 0x95, 0x97, 0x94, 0x91, 0x8A, 0x85, 0x7F, 0x7B, 0x79, 0x7D, 0x7D,
	0x7F, 0x80, 0x80, 0x82, 0x7E, 0x7C, 0x77, 0x74, 0x6E, 0x69, 0x6C, 0x6D,
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
};
