AhmadHaniF1145/Projek-Mikrokontroller-Sensor-Gas/ProgramUtama/Program Utama_Bare Metal_PlatformIO/src/audio2.h

#include <Arduino.h>

const unsigned char audio2[] PROGMEM = {
0x82, 0x81, 0x7F, 0x7D, 0x7B, 0x7A, 0x79, 0x77, 0x76, 0x76, 0x76, 0x76,
	0x76, 0x77, 0x78, 0x7A, 0x7B, 0x7D, 0x80, 0x81, 0x83, 0x85, 0x86, 0x87,
	0x88, 0x89, 0x89, 0x89, 0x88, 0x88, 0x86, 0x84, 0x83, 0x81, 0x7F, 0x7D,
	0x7B, 0x79, 0x78, 0x76, 0x75, 0x75, 0x76, 0x76, 0x77, 0x78, 0x79, 0x7B,
	0x7E, 0x80, 0x81, 0x83, 0x84, 0x86, 0x88, 0x89, 0x89, 0x8A, 0x89, 0x89,
	0x89, 0x88, 0x86, 0x85, 0x82, 0x80, 0x7F, 0x7C, 0x7A, 0x78, 0x76, 0x76,
	0x75, 0x75, 0x75, 0x75, 0x76, 0x78, 0x79, 0x7B, 0x7E, 0x80, 0x81, 0x83,
	0x85, 0x87, 0x89, 0x89, 0x8A, 0x8A, 0x8A, 0x8A, 0x89, 0x87, 0x85, 0x84,
	0x82, 0x80, 0x7E, 0x7B, 0x79, 0x77, 0x76, 0x75, 0x75, 0x75, 0x75, 0x76,
	0x77, 0x78, 0x7A, 0x7C, 0x7E, 0x80, 0x82, 0x84, 0x86, 0x87, 0x89, 0x89,
	0x8A, 0x8A, 0x8A, 0x89, 0x88, 0x86, 0x84, 0x83, 0x80, 0x7E, 0x7C, 0x7A,
	0x78, 0x77, 0x76, 0x75, 0x75, 0x75, 0x75, 0x76, 0x77, 0x79, 0x7B, 0x7D,
	0x7F, 0x81, 0x83, 0x85, 0x87, 0x88, 0x8A, 0x8A, 0x8B, 0x8B, 0x8A, 0x89,
	0x87, 0x86, 0x84, 0x82, 0x80, 0x7E, 0x7C, 0x79, 0x78, 0x76, 0x75, 0x75,
	0x75, 0x75, 0x75, 0x76, 0x78, 0x79, 0x7B, 0x7D, 0x80, 0x82, 0x84, 0x86,
	0x87, 0x89, 0x8A, 0x8A, 0x8A, 0x8A, 0x89, 0x89, 0x87, 0x85, 0x83, 0x81,
	0x7F, 0x7D, 0x7B, 0x79, 0x77, 0x76, 0x75, 0x74, 0x74, 0x75, 0x75, 0x77,
	0x78, 0x79, 0x7B, 0x7D, 0x7F, 0x82, 0x84, 0x85, 0x87, 0x88, 0x8A, 0x8A,
	0x8A, 0x8A, 0x8A, 0x89, 0x88, 0x86, 0x84, 0x82, 0x80, 0x7E, 0x7C, 0x7A,
	0x78, 0x76, 0x75, 0x75, 0x74, 0x75, 0x75, 0x76, 0x77, 0x78, 0x7A, 0x7C,
	0x7E, 0x80, 0x82, 0x84, 0x86, 0x87, 0x88, 0x89, 0x8A, 0x8A, 0x8A, 0x89,
	0x88, 0x87, 0x85, 0x84, 0x82, 0x80, 0x7E, 0x7C, 0x7A, 0x79, 0x78, 0x77,
	0x76, 0x76, 0x76, 0x76, 0x77, 0x78, 0x79, 0x7A, 0x7C, 0x7E, 0x80, 0x81,
	0x83, 0x85, 0x87, 0x88, 0x89, 0x8A, 0x8A, 0x8A, 0x8A, 0x89, 0x88, 0x86,
	0x85, 0x82, 0x80, 0x7E, 0x7C, 0x7A, 0x79, 0x77, 0x76, 0x75, 0x75, 0x75,
	0x75, 0x76, 0x77, 0x78, 0x79, 0x7B, 0x7D, 0x7F, 0x80, 0x83, 0x85, 0x86,
	0x88, 0x8C, 0x8D, 0x8D, 0x8D, 0x8C, 0x8C, 0x8B, 0x8B, 0x8A, 0x86, 0x82,
	0x7F, 0x7D, 0x7A, 0x76, 0x76, 0x76, 0x71, 0x6D, 0x6B, 0x6A, 0x69, 0x6A,
	0x6A, 0x6C, 0x73, 0x7C, 0x84, 0x8A, 0x91, 0x98, 0x9E, 0xA0, 0x9B, 0x93,
	0x8C, 0x86, 0x81, 0x7B, 0x75, 0x72, 0x73, 0x72, 0x72, 0x73, 0x75, 0x77,
	0x78, 0x75, 0x73, 0x71, 0x72, 0x75, 0x75, 0x80, 0x93, 0x9F, 0xA3, 0x9E,
	0x91, 0x89, 0x89, 0x82, 0x7D, 0x7F, 0x82, 0x8C, 0x8F, 0x83, 0x78, 0x74,
	0x73, 0x76, 0x72, 0x69, 0x66, 0x66, 0x63, 0x60, 0x63, 0x6B, 0x79, 0x82,
	0x8F, 0xA2, 0xAD, 0xAE, 0xA5, 0x92, 0x85, 0x7E, 0x75, 0x72, 0x74, 0x79,
	0x8C, 0x9C, 0xA3, 0xA0, 0x8F, 0x7F, 0x74, 0x6F, 0x6B, 0x6B, 0x67, 0x66,
	0x68, 0x6A, 0x6B, 0x6C, 0x70, 0x76, 0x7C, 0x7A, 0x82, 0x91, 0x9B, 0x9D,
	0x94, 0x86, 0x80, 0x7F, 0x7D, 0x7B, 0x7B, 0x7C, 0x84, 0x94, 0x95, 0x94,
	0x8D, 0x7E, 0x75, 0x71, 0x6C, 0x6E, 0x72, 0x6F, 0x6F, 0x6F, 0x6B, 0x68,
	0x6A, 0x6D, 0x72, 0x77, 0x79, 0x7E, 0x92, 0xA3, 0xAB, 0xA7, 0x9D, 0x91,
	0x8B, 0x84, 0x7B, 0x79, 0x7B, 0x82, 0x8A, 0x91, 0x95, 0x96, 0x99, 0x91,
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
};
